trope-oshw/anthracite/docs/schematics/anthracite-bottom-A1.png

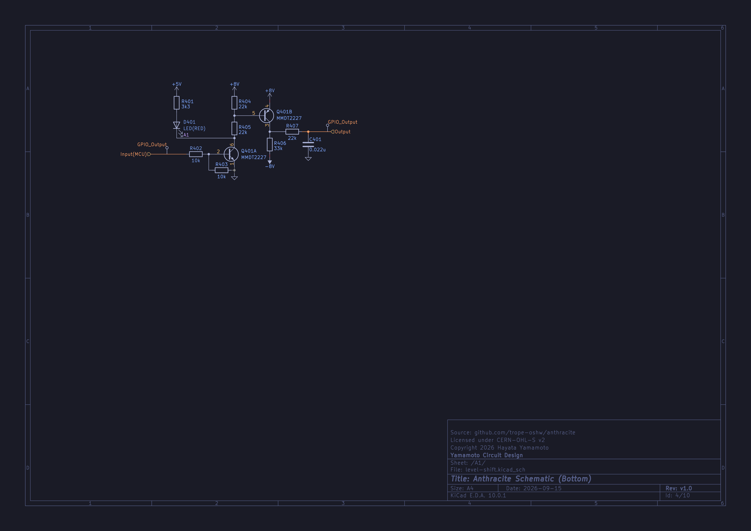
docs/schematics/anthracite-bottom-A1.png
