trope-oshw/anthracite/enclosure/panel-artwork.png

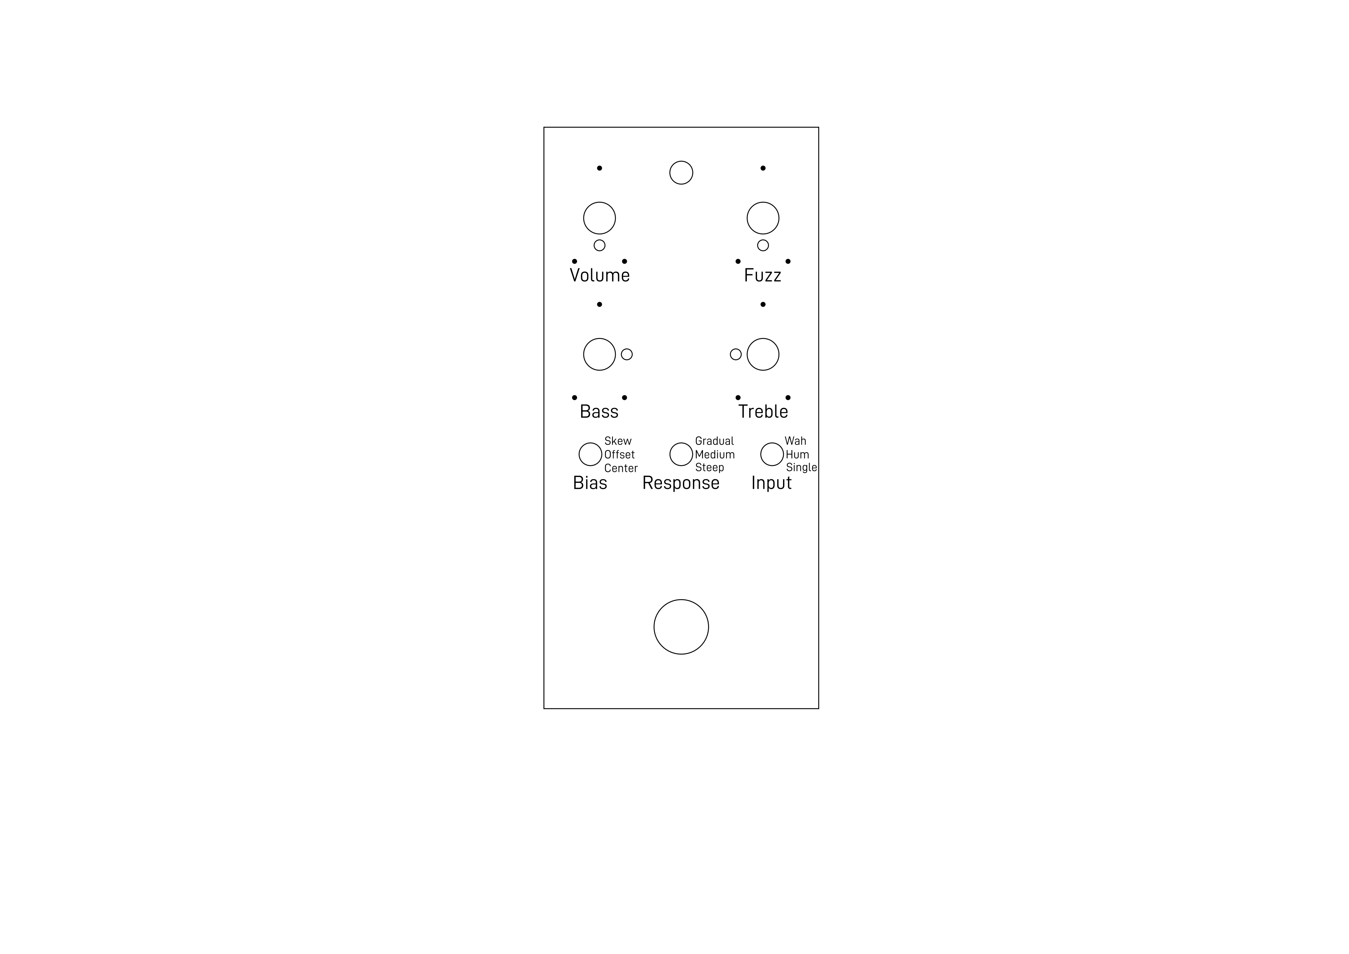
enclosure/panel-artwork.png
